rgodin974/ESP32_sprinkler_timer/KiCAD/3D/G2RL_1.step

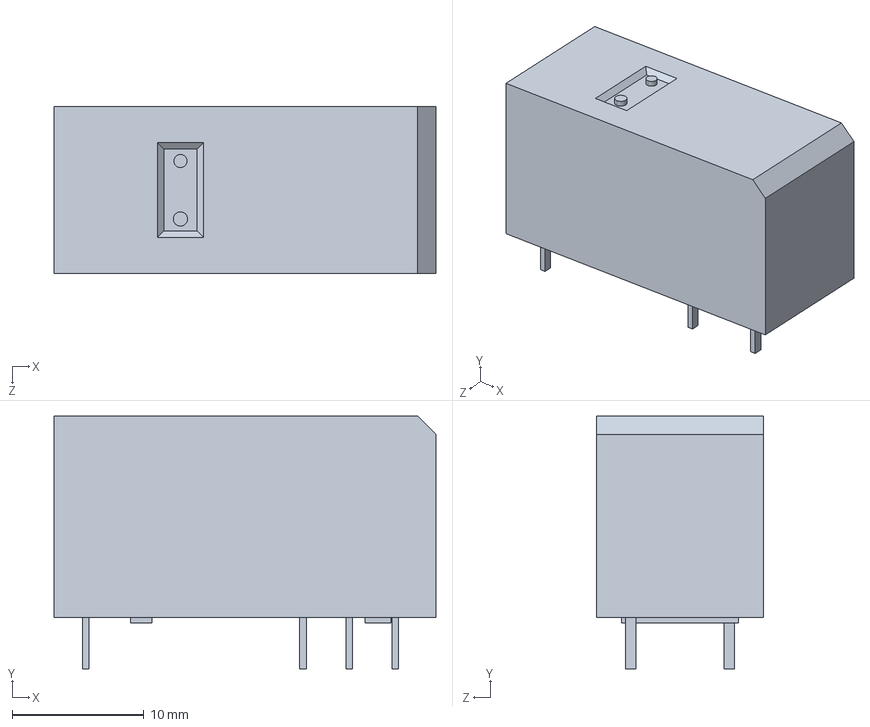
[picture p20: CAD file, 2024-05-24]
KiCAD/3D/G2RL_1.step
29.0 x 19.2 x 12.7 mm
