rgodin974/ESP32_sprinkler_timer/KiCAD/3D/HLK-10M024.step

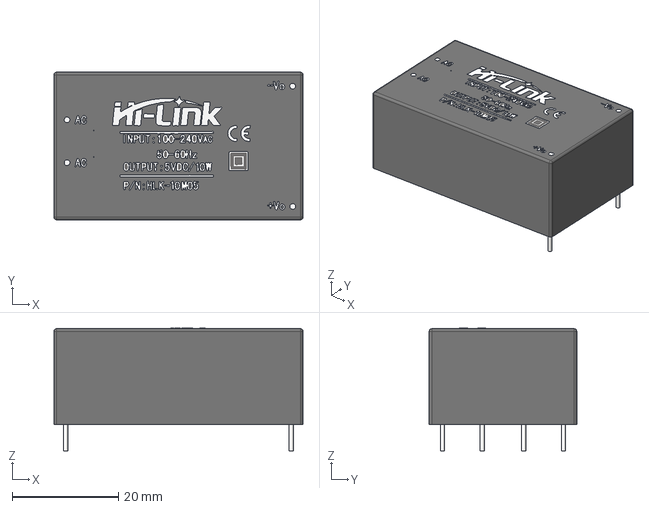
[picture p21: CAD file, 2024-05-24]
KiCAD/3D/HLK-10M024.step
46.9 x 27.8 x 23.1 mm
