rgodin974/ESP32_sprinkler_timer/include/constants.h

// Max line length in config file
#define MAX_LINE        250

// Max definition length for object names (relays, ways, zones, etc.)
#define MAX_DEF         50
#define MAX_BUF         30

// Max ways and relays number
#define MAX_WAY         8

// Max zones number
#define MAX_ZONE        2

// Max waterings number in a day for each way
#define MAX_SCHEDULE    4

// Max waterings number in a day for all ways
#define MAX_WATERING    24

// Main valve open-time
#define OPEN_TIME       20

// Humidity sensor 
#define HUMIDITY_AIR    2400
#define HUMIDITY_WATER  1850
