rgodin974/ESP32_sprinkler_timer/include/html.h

#ifndef _HTML_H_
#define _HTML_H_

#include <ESPAsyncWebServer.h>
#include <SPIFFS.h>
#include "way.h"

extern AsyncWebServer server;

void handleRoot(AsyncWebServerRequest *request);
void handleEdit(AsyncWebServerRequest *request);
void handleEditSubmit(AsyncWebServerRequest *request);
void handleAdd(AsyncWebServerRequest *request);
void handleRemove(AsyncWebServerRequest *request);
void handleWeather(AsyncWebServerRequest *request);

String templateProcessor(const String& var);
void initWebSocket();
void cleanUpClient();
void notifyClients(String JSON_Data);
void handleWebSocketMessage(void *arg, uint8_t *data, size_t len);
void onEvent(AsyncWebSocket *server, AsyncWebSocketClient *client, AwsEventType type, void *arg, uint8_t *data, size_t len);
void htmlCreateWifi(String &message);
void htmlCreateValve(String &message);
void htmlCreateRelays(String &message);
void htmlCreateWaterings(String &message);
void updateWebSocketData(const char *op);
void updateWebSocketData(const char *op, Way *way);
void updateWebSocketData(const char *op, Relay *relay);
void updateWebSocketData(const char *op, Watering *w);

#endif
