rgodin974/ESP32_sprinkler_timer/include/weather.h

#ifndef _WEATHER_H_
#define _WEATHER_H_

#pragma once
#include <JsonListener.h>
#include <JsonStreamingParser.h>

typedef struct OpenWeatherMapCurrentData {
  // "lon": 8.54,
  float lon;
  // "lat": 47.37
  float lat;
  // "id": 521,
  uint16_t weatherId;
  // "main": "Rain",
  String main;
  // "description": "shower rain",
  String description;
  // "icon": "09d"
  String icon;
  String iconMeteoCon;
  // "temp": 290.56,
  float temp;
  // feels_like	290.87
  float feelsLike;
  // "pressure": 1013,
  uint16_t pressure;
  // "humidity": 87,
  uint8_t humidity;
  // "temp_min": 289.15,
  float tempMin;
  // "temp_max": 292.15
  float tempMax;
  // visibility: 10000,
  uint16_t visibility;
  // "wind": {"speed": 1.5},
  float windSpeed;
  // "wind": {deg: 226.505},
  float windDeg;
  // "clouds": {"all": 90},
  uint8_t clouds;
  // "dt": 1527015000,
  uint32_t observationTime;
  // "country": "CH",
  String country;
  // "sunrise": 1526960448,
  uint32_t sunrise;
  // "sunset": 1527015901
  uint32_t sunset;
  // "name": "Zurich",
  String cityName;
} OpenWeatherMapCurrentData;

class OpenWeatherMapCurrent: public JsonListener {
  private:
    const String host = "api.openweathermap.org";
    const uint8_t port = 80;
    String currentKey;
    String currentParent;
    OpenWeatherMapCurrentData *data;
    uint8_t weatherItemCounter = 0;
    boolean metric = true;
    String language;

    void doUpdate(OpenWeatherMapCurrentData *data, String path);
    String buildPath(String appId, String locationParameter);

  public:
    OpenWeatherMapCurrent();
    void updateCurrent(OpenWeatherMapCurrentData *data, String appId, String location);
    void updateCurrentById(OpenWeatherMapCurrentData *data, String appId, String locationId);

    void setMetric(boolean metric) {this->metric = metric;}
    boolean isMetric() { return metric; }
    void setLanguage(String language) { this->language = language; }
    String getLanguage() { return language; }
    
    String getMeteoconIcon(String icon);
    virtual void whitespace(char c);

    virtual void startDocument();

    virtual void key(String key);

    virtual void value(String value);

    virtual void endArray();

    virtual void endObject();

    virtual void endDocument();

    virtual void startArray();

    virtual void startObject();
};

#endif
